FablabRobertHoudin/32x32-matrix/ESP_32x32/custom sample.c

const char* ssid2 = "ssid1";
const char* password2 = "pass1";
const char* ssid1 = "ssid2";
const char* password1 = "pass2";


const char* pubKey = "pub-c-XXXXXXXXXXXXXXXXXXXXXXXXXXXXXXXXXXXX";
const char* subKey = "sub-c-XXXXXXXXXXXXXXXXXXXXXXXXXXXXXXXXXXXX";
